flooklab/Lightning_Detector/Firmware/lightning_detector/auxil.cpp

/*
////////////////////////////////////////////////////////////////////////////////////
//
//  This file is part of the firmware of Lightning Detector, an experimental open
//  hardware project for early notification about approaching thunderstorm activity.
//  Copyright (C) 2024–2025 M. Frohne
//
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
////////////////////////////////////////////////////////////////////////////////////
*/

#include "auxil.h"

#include <functional>

namespace Auxil
{

/*!
 * \brief Estimate the battery percentage.
 *
 * Estimates the battery charge from the measured voltage using an approximate look-up table
 * that was matched to \p CR2032 discharge curves available online. This takes into account
 * - the battery's changing internal resistance and number of parallel batteries (\p pNumCoinCells),
 * - the expected load current during the voltage measurement (\p pLoadCurrentIdle),
 * - the maximum expected current to determine a conservative 0 percent value (\p pLoadCurrentMax).
 *
 * The charge state when the voltage would drop below \p pLowVoltage given a load current
 * of \p pLoadCurrentMax results in a return value of 0, while a full battery under an
 * "idle" load current of \p pLoadCurrentIdle should yield a return value of 100.
 *
 * \param pCurrentVoltage Currently measured voltage in idle state.
 * \param pHighVoltage Maximum open-circuit battery voltage (i.e. ~ nominal voltage).
 * \param pLowVoltage Minimum required voltage.
 * \param pLoadCurrentIdle Approximate idle state current.
 * \param pLoadCurrentMax Approximate maximum current.
 * \param pNumCoinCells Number of parallel batteries used.
 * \return Estimated percentage value of remaining battery charge.
 */
float calcBatteryPercentage(float pCurrentVoltage, float pHighVoltage, float pLowVoltage,
                            float pLoadCurrentIdle, float pLoadCurrentMax, size_t pNumCoinCells)
{
    constexpr float chargeStateLUT[] = {3.000000, 2.999624, 2.999248, 2.998872, 2.998495, 2.998120, 2.997743, 2.997367, 2.996990,
        2.996614, 2.996237, 2.995861, 2.995484, 2.995107, 2.994730, 2.994353, 2.993976, 2.993599, 2.993221, 2.992844, 2.992466,
        2.992089, 2.991711, 2.991334, 2.990955, 2.990578, 2.990199, 2.989821, 2.989442, 2.989064, 2.988685, 2.988306, 2.987926,
        2.987548, 2.987168, 2.986789, 2.986408, 2.986029, 2.985648, 2.985269, 2.984888, 2.984507, 2.984126, 2.983745, 2.983363,
        2.982982, 2.982600, 2.982218, 2.981835, 2.981453, 2.981070, 2.980687, 2.980304, 2.979919, 2.979536, 2.979151, 2.978767,
        2.978381, 2.977996, 2.977610, 2.977224, 2.976837, 2.976450, 2.976062, 2.975675, 2.975286, 2.974898, 2.974508, 2.974118,
        2.973728, 2.973337, 2.972946, 2.972554, 2.972161, 2.971769, 2.971374, 2.970981, 2.970585, 2.970190, 2.969793, 2.969397,
        2.968998, 2.968600, 2.968200, 2.967801, 2.967399, 2.966998, 2.966594, 2.966191, 2.965786, 2.965381, 2.964974, 2.964566,
        2.964157, 2.963748, 2.963336, 2.962924, 2.962510, 2.962096, 2.961679, 2.961262, 2.960844, 2.960423, 2.960002, 2.959578,
        2.959153, 2.958726, 2.958298, 2.957868, 2.957436, 2.957002, 2.956567, 2.956129, 2.955689, 2.955247, 2.954804, 2.954357,
        2.953909, 2.953457, 2.953004, 2.952547, 2.952089, 2.951627, 2.951163, 2.950696, 2.950226, 2.949752, 2.949276, 2.948796,
        2.948313, 2.947826, 2.947336, 2.946841, 2.946343, 2.945841, 2.945335, 2.944824, 2.944309, 2.943789, 2.943266, 2.942736,
        2.942202, 2.941663, 2.941119, 2.940568, 2.940013, 2.939451, 2.938883, 2.938309, 2.937729, 2.937142, 2.936548, 2.935947,
        2.935338, 2.934723, 2.934098, 2.933467, 2.932826, 2.932178, 2.931520, 2.930853, 2.930176, 2.929491, 2.928794, 2.928088,
        2.927370, 2.926642, 2.925901, 2.925150, 2.924385, 2.923609, 2.922819, 2.922017, 2.921199, 2.920368, 2.919522, 2.918661,
        2.917783, 2.916890, 2.915980, 2.915053, 2.914107, 2.913144, 2.912160, 2.911158, 2.910135, 2.909091, 2.908025, 2.906938,
        2.905827, 2.904692, 2.903532, 2.902348, 2.901137, 2.899899, 2.898633, 2.897338, 2.896013, 2.894658, 2.893271, 2.891852,
        2.890398, 2.888909, 2.887385, 2.885823, 2.884223, 2.882583, 2.880903, 2.879180, 2.877413, 2.875601, 2.873744, 2.871837,
        2.869882, 2.867875, 2.865816, 2.863701, 2.861532, 2.859303, 2.857015, 2.854664, 2.852251, 2.849770, 2.847222, 2.844603,
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
        31.74685, 32.25345, 32.77545, 33.31344, 33.86791, 34.43947, 35.02850, 35.63571, 36.26169, 36.90694, 37.57215, 38.25792,
        38.96494, 39.69401, 40.44572, 41.22078, 42.01996, 42.84418, 43.69401, 44.57046, 45.47443, 46.40659, 47.36806, 48.35962,
        49.38246, 50.43738, 51.52547, 52.64783, 53.80564, 55.00000, 56.23200, 57.50293, 58.81398, 60.16665, 61.56202, 63.00169,
        64.48694, 66.01937, 67.60036, 69.23160, 70.91469, 72.65121, 74.44304, 76.29189, 78.19962, 80.16804, 82.19932, 84.29526,
        86.45814, 88.68994, 90.99305, 93.36975, 95.82243, 98.35336};

    auto findChargeState = [chargeStateLUT = std::cref(chargeStateLUT), innerResistanceLUT = std::cref(innerResistanceLUT),
                            lutLength, pNumCoinCells](float pVoltage, float pLoadCurrent) -> size_t
    {
        for (size_t i = 0; i < lutLength; ++i)
            if ((chargeStateLUT[i] - pLoadCurrent*innerResistanceLUT[i]/pNumCoinCells) < pVoltage)
                return i;

        return lutLength;
    };

    size_t highChargeIdx = findChargeState(pHighVoltage, 0);
    size_t currentChargeIdx = findChargeState(pCurrentVoltage, pLoadCurrentIdle);
    size_t lowChargeIdx = findChargeState(pLowVoltage, pLoadCurrentMax);

    if (currentChargeIdx < highChargeIdx)
        currentChargeIdx = highChargeIdx;
    else if (currentChargeIdx > lowChargeIdx)
        currentChargeIdx = lowChargeIdx;

    return 100. * (static_cast<float>(lowChargeIdx - currentChargeIdx) / static_cast<float>(lowChargeIdx - highChargeIdx));
}

} // namespace Auxil
